piep-projects/TempSensorEmulator/src/display.cpp

#include "display.h"
#include "config.h"
#include <LovyanGFX.hpp>
#include <LittleFS.h>

// ── LovyanGFX: T-Display-S3, ST7789V, 8080-Parallelbus ────────
class LGFX : public lgfx::LGFX_Device {
    lgfx::Panel_ST7789   _panel;
    lgfx::Bus_Parallel8  _bus;
    lgfx::Light_PWM      _light;
public:
    LGFX() {
        {
            auto cfg       = _bus.config();
            cfg.pin_wr     = PIN_LCD_WR;
            cfg.pin_rd     = PIN_LCD_RD;
            cfg.pin_rs     = PIN_LCD_DC;
            cfg.pin_d0     = PIN_LCD_D0;
            cfg.pin_d1     = PIN_LCD_D1;
            cfg.pin_d2     = PIN_LCD_D2;
            cfg.pin_d3     = PIN_LCD_D3;
            cfg.pin_d4     = PIN_LCD_D4;
            cfg.pin_d5     = PIN_LCD_D5;
            cfg.pin_d6     = PIN_LCD_D6;
            cfg.pin_d7     = PIN_LCD_D7;
            cfg.freq_write = 20000000;
            _bus.config(cfg);
            _panel.setBus(&_bus);
        }
        {
            auto cfg          = _panel.config();
            cfg.pin_cs        = PIN_LCD_CS;
            cfg.pin_rst       = PIN_LCD_RST;
            cfg.pin_busy      = -1;
            cfg.panel_width   = 170;
            cfg.panel_height  = 320;
            cfg.offset_x      = 35;
            cfg.offset_y      = 0;
            cfg.invert        = true;
            _panel.config(cfg);
        }
        {
            auto cfg        = _light.config();
            cfg.pin_bl      = PIN_LCD_BL;
            cfg.invert      = false;
            cfg.freq        = 44100;
            cfg.pwm_channel = 7;
            _light.config(cfg);
            _panel.setLight(&_light);
        }
        setPanel(&_panel);
    }
};

static LGFX tft;

// ── Farben ────────────────────────────────────────────────────
static constexpr uint32_t COL_BG       = 0x000000u;
static constexpr uint32_t COL_WHITE    = 0xFFFFFFu;
static constexpr uint32_t COL_YELLOW   = 0xFFDC00u;
static constexpr uint32_t COL_GREEN    = 0x00C850u;
static constexpr uint32_t COL_RED      = 0xDC3232u;
static constexpr uint32_t COL_ORANGE   = 0xFF9600u;
static constexpr uint32_t COL_DKGREY   = 0x505050u;
static constexpr uint32_t COL_MIDGREY  = 0x8C8C8Cu;
static constexpr uint32_t COL_LTBLUE   = 0x50A0FFu;
static constexpr uint32_t COL_SEP      = 0x282828u;
static constexpr uint32_t COL_SEP_YEL  = 0x504000u;
static constexpr uint32_t COL_SEP_BLU  = 0x1E3C78u;

// ── Hilfsfunktionen ──────────────────────────────────────────

static void drawSeparator(int y, uint32_t col = COL_SEP) {
    tft.drawFastHLine(0, y, 320, col);
}

// Batterie-Icon bei (x,y), Breite 27px, Höhe 14px
static void drawBatIcon(int x, int y, int pct, bool charging) {
    uint32_t fillColor = pct < BAT_WARN_PCT ? COL_RED :
                         pct < 30           ? COL_ORANGE : COL_GREEN;
    tft.drawRect(x, y, 24, 14, COL_MIDGREY);
    tft.fillRect(x + 24, y + 4, 3, 6, COL_MIDGREY);
    int fw = constrain((pct * 22) / 100, 0, 22);
    if (fw > 0) tft.fillRect(x + 1, y + 1, fw, 12, fillColor);
    if (charging) {
        tft.setTextColor(COL_YELLOW);
        tft.setFont(&fonts::Font0);
        tft.setCursor(x + 28, y + 3);
        tft.print("+");
    }
}

// WiFi-Balken (3 Stufen) bei (x,y), Breite ~11px, Höhe 14px
static void drawWifiIcon(int x, int y, bool connected) {
    uint32_t c = connected ? COL_WHITE : COL_DKGREY;
    tft.fillRect(x,      y + 8, 3, 6,  c);
    tft.fillRect(x + 4,  y + 4, 3, 10, c);
    tft.fillRect(x + 8,  y,     3, 14, c);
}

// Logo aus LittleFS zeichnen (PNG, weiß auf schwarz)
static void drawLogo(int x, int y, int maxW, int maxH) {
    File f = LittleFS.open("/logo.png");
    if (!f) return;
    size_t sz = f.size();
    uint8_t* buf = (uint8_t*)malloc(sz);
    if (!buf) { f.close(); return; }
    f.read(buf, sz);
    f.close();
    tft.drawPng(buf, sz, x, y, maxW, maxH);
    free(buf);
}

// Zentrierten Text zeichnen; gibt die tatsächliche Textbreite zurück
static int drawCentered(const char* txt, int y,
                         const lgfx::IFont* font, uint32_t col) {
    tft.setFont(font);
    tft.setTextColor(col);
    int tw = tft.textWidth(txt);
    tft.drawString(txt, (320 - tw) / 2, y);
    return tw;
}

// ── Öffentliche API ───────────────────────────────────────────

void displayBegin() {
    pinMode(PIN_POWER_ON, OUTPUT);
    digitalWrite(PIN_POWER_ON, HIGH);

    tft.init();
    tft.setRotation(1);   // Querformat 320×170
    tft.setBrightness(180);
    tft.fillScreen(COL_BG);

    LittleFS.begin(true);
}

void displayBrightness(uint8_t val) {
    tft.setBrightness(val);
}

// ── SCREEN 1: Splash ─────────────────────────────────────────
void drawSplash() {
    tft.fillScreen(COL_BG);

    // Logo: explizite Skalierung 0.46 → 260×158 wird zu 120×73 px
    // maxW/maxH nicht verwendet, da maxW > PNG-Breite LovyanGFX zum
    // Hochskalieren veranlasst und das Logo den Text überdeckt.
    {
        File f = LittleFS.open("/logo.png");
        if (f) {
            size_t sz = f.size();
            uint8_t* buf = (uint8_t*)malloc(sz);
            if (buf) {
                f.read(buf, sz);
                // Zentriert: x = (320-120)/2 = 100, y=8, Unterrand y≈81
                tft.drawPng(buf, sz, 100, 8, 0, 0, 0, 0, 0.46f, 0.46f);
                free(buf);
            }
            f.close();
        }
    }

    // "TempSensorEmulator" in Gelb (11 px Abstand zum Logo-Unterrand)
    tft.setFont(&fonts::Font4);
    tft.setTextSize(1);
    tft.setTextColor(COL_YELLOW);
    String title = "TempSensorEmulator";
    int tw = tft.textWidth(title);
    tft.drawString(title, (320 - tw) / 2, 92);

    // Firmware-Version in Dunkelgrau
    tft.setFont(&fonts::Font2);
    tft.setTextSize(1);
    tft.setTextColor(COL_DKGREY);
    String ver = FW_VERSION;
    tw = tft.textWidth(ver);
    tft.drawString(ver, (320 - tw) / 2, 112);
}

// ── SCREEN 2: Hauptscreen ─────────────────────────────────────
void drawMain(float tempC, float ohm,
              int batPct, bool charging,
              const char* wifiIP, bool i2cOk) {
    tft.fillScreen(COL_BG);
    tft.setTextSize(1);

    // ── Statusleiste (y 0–25) ────────────────────────────────
    tft.setFont(&fonts::Font2);
    tft.setTextColor(COL_YELLOW);
    tft.drawString("TempSensorEmulator", 4, 9);

    bool connected = (wifiIP[0] != '-' && wifiIP[0] != 'A');
    drawWifiIcon(175, 6, connected);

    drawBatIcon(191, 6, batPct, charging);
    tft.setTextColor(batPct < BAT_WARN_PCT ? COL_RED : COL_WHITE);
    char buf[8];
    snprintf(buf, sizeof(buf), "%d%%", batPct);
    tft.drawString(buf, 220, 9);

    drawSeparator(26);

    // ── Tasten-Hint oben rechts: KEY = Temp + ────────────────
    tft.setFont(&fonts::Font2);
    tft.setTextColor(COL_YELLOW);
    const char* hP1 = "Temp +";
    tft.drawString(hP1, 320 - tft.textWidth(hP1) - 4, 28);
    tft.setTextColor(COL_WHITE);
    const char* hP2 = "lang: AUS";
    tft.drawString(hP2, 320 - tft.textWidth(hP2) - 4, 47);

    // ── Temperatur zentriert (y 63–111) ──────────────────────
    char tmpBuf[10];
    snprintf(tmpBuf, sizeof(tmpBuf), "%.1f", tempC);

    tft.setFont(&fonts::Font7);
    int tw = tft.textWidth(tmpBuf);
    int tx = (260 - tw) / 2;   // in 260px-Zone links (rechts 60px für Hints)
    if (tx < 4) tx = 4;
    int ty = 63;

    tft.setTextColor(COL_WHITE);
    tft.drawString(tmpBuf, tx, ty);

    // "oC" in Gelb, Font4×2 (32px) — bottom-aligned mit Temperatur
    // Font6 enthält nur Ziffern+Doppelpunkt, daher Font4 bei size 2
    // Grad-Symbol: nur kleines "o" (Font4×1)
    tft.setFont(&fonts::Font4);
    tft.setTextColor(COL_YELLOW);
    tft.setTextSize(1);
    tft.drawString("o", tx + tw + 6, ty - 10);

    // ── Tasten-Hint unten rechts: BOOT = Temp − ──────────────
    tft.setFont(&fonts::Font2);
    tft.setTextColor(COL_YELLOW);
    const char* hM1 = "Temp -";
    tft.drawString(hM1, 320 - tft.textWidth(hM1) - 4, 110);
    tft.setTextColor(COL_WHITE);
    const char* hM2 = "lang: WLAN";
    tft.drawString(hM2, 320 - tft.textWidth(hM2) - 4, 129);

    drawSeparator(148);

    // ── Info-Zeile: R-Wert + I²C-Statusblock ─────────────────
    tft.setFont(&fonts::Font2);
    char info[24];
    snprintf(info, sizeof(info), "R = %.0f Ohm", ohm);
    tft.setTextColor(COL_YELLOW);
    tft.drawString(info, 4, 153);

    int rw = tft.textWidth(info);
    int bx = 4 + rw + 6;
    tft.setTextColor(i2cOk ? COL_GREEN : COL_RED);
    tft.drawString("I2C", bx, 153);
}

// ── SCREEN 3: WiFi-Setup ─────────────────────────────────────
void drawWifiSetup(const char* ip) {
    tft.fillScreen(COL_BG);
    tft.setTextSize(1);

    // Blauer Rahmen
    tft.drawRect(4, 4, 312, 162, COL_LTBLUE);

    // ── Titel Header (kein Logo) ──────────────────────────────
    tft.setFont(&fonts::Font2);
    tft.setTextColor(COL_YELLOW);
    tft.drawString("TempSensorEmulator", 10, 10);

    drawSeparator(28, COL_SEP_BLU);

    // ── "WiFi-Konfiguration" linksbündig ─────────────────────
    tft.setFont(&fonts::Font4);
    tft.setTextColor(COL_LTBLUE);
    tft.setTextSize(1);
    tft.drawString("WiFi-Konfiguration", 10, 34);

    drawSeparator(54, COL_SEP_BLU);

    // SSID und Passwort
    drawWifiIcon(14, 62, true);
    tft.setFont(&fonts::Font2);
    tft.setTextColor(COL_WHITE);
    tft.drawString("AP:  " WIFI_AP_SSID, 30, 60);
    tft.setTextColor(COL_MIDGREY);
    tft.drawString("PW:  " WIFI_AP_PASS, 30, 74);

    drawSeparator(88, COL_SEP_BLU);

    // Schritt-für-Schritt
    tft.setFont(&fonts::Font2);
    tft.setTextColor(COL_MIDGREY);
    tft.drawString("1.  Handy mit  \"" WIFI_AP_SSID "\"  verbinden", 12, 96);
    tft.drawString("2.  Browser oeffnet sich automatisch",          12, 110);
    tft.drawString("3.  Heimnetz waehlen + Passwort eingeben",      12, 124);

    drawSeparator(140, COL_SEP_BLU);

    // IP nach Verbindung (gelb, linksbündig) oder Warte-Text
    tft.setFont(&fonts::Font2);
    if (ip && ip[0]) {
        char ipLine[48];
        snprintf(ipLine, sizeof(ipLine), "Verbunden: %s", ip);
        tft.setTextColor(COL_YELLOW);
        tft.drawString(ipLine, 10, 146);
    } else {
        tft.setTextColor(COL_DKGREY);
        drawCentered("Warte auf Verbindung ...", 146, &fonts::Font2, COL_DKGREY);
    }
}

// ── SCREEN 4: Shutdown (mit Countdown) ───────────────────────
void drawShutdown(float tempC, int countdownSec) {
    tft.fillScreen(COL_BG);
    tft.setTextSize(1);

    // Gelber Rahmen
    tft.drawRect(4, 4, 312, 162, COL_YELLOW);

    // ── Titel Header (kein Logo) ──────────────────────────────
    tft.setFont(&fonts::Font2);
    tft.setTextColor(COL_YELLOW);
    tft.drawString("TempSensorEmulator", 10, 10);

    drawSeparator(28, COL_SEP_YEL);

    drawCentered("... wird ausgeschaltet", 34, &fonts::Font4, COL_YELLOW);

    drawSeparator(56, COL_SEP_YEL);

    // Letzte Temperatur — Text + "o" separat für Superscript-Position
    tft.setFont(&fonts::Font2);
    char buf[40];
    snprintf(buf, sizeof(buf), "Letzte Temperatur:  %.1f", tempC);
    int lw = tft.textWidth(buf);
    int lx = (320 - lw) / 2;
    tft.setTextColor(COL_MIDGREY);
    tft.drawString(buf, lx, 62);
    tft.drawString("o", lx + lw + 2, 58);
    drawCentered("wurde gespeichert.", 76, &fonts::Font2, COL_MIDGREY);

    drawSeparator(92, COL_SEP_YEL);

    // Wichtiger Hinweis
    drawCentered("Bitte echten Fuehler wieder",  98, &fonts::Font2, COL_YELLOW);
    drawCentered("an Heizung anschliessen!", 112, &fonts::Font2, COL_YELLOW);

    drawSeparator(128, COL_SEP_YEL);

    // Countdown
    char cdBuf[24];
    snprintf(cdBuf, sizeof(cdBuf), "Ausschalten in  %d s ...", countdownSec);
    drawCentered(cdBuf, 136, &fonts::Font2, COL_DKGREY);
}
